vrunk11/DomesdayDuplicator/hardware/pcb/ADC.kicad_sch

## KiCad design hardware/pcb/ADC.kicad_sch (2026-08-29)

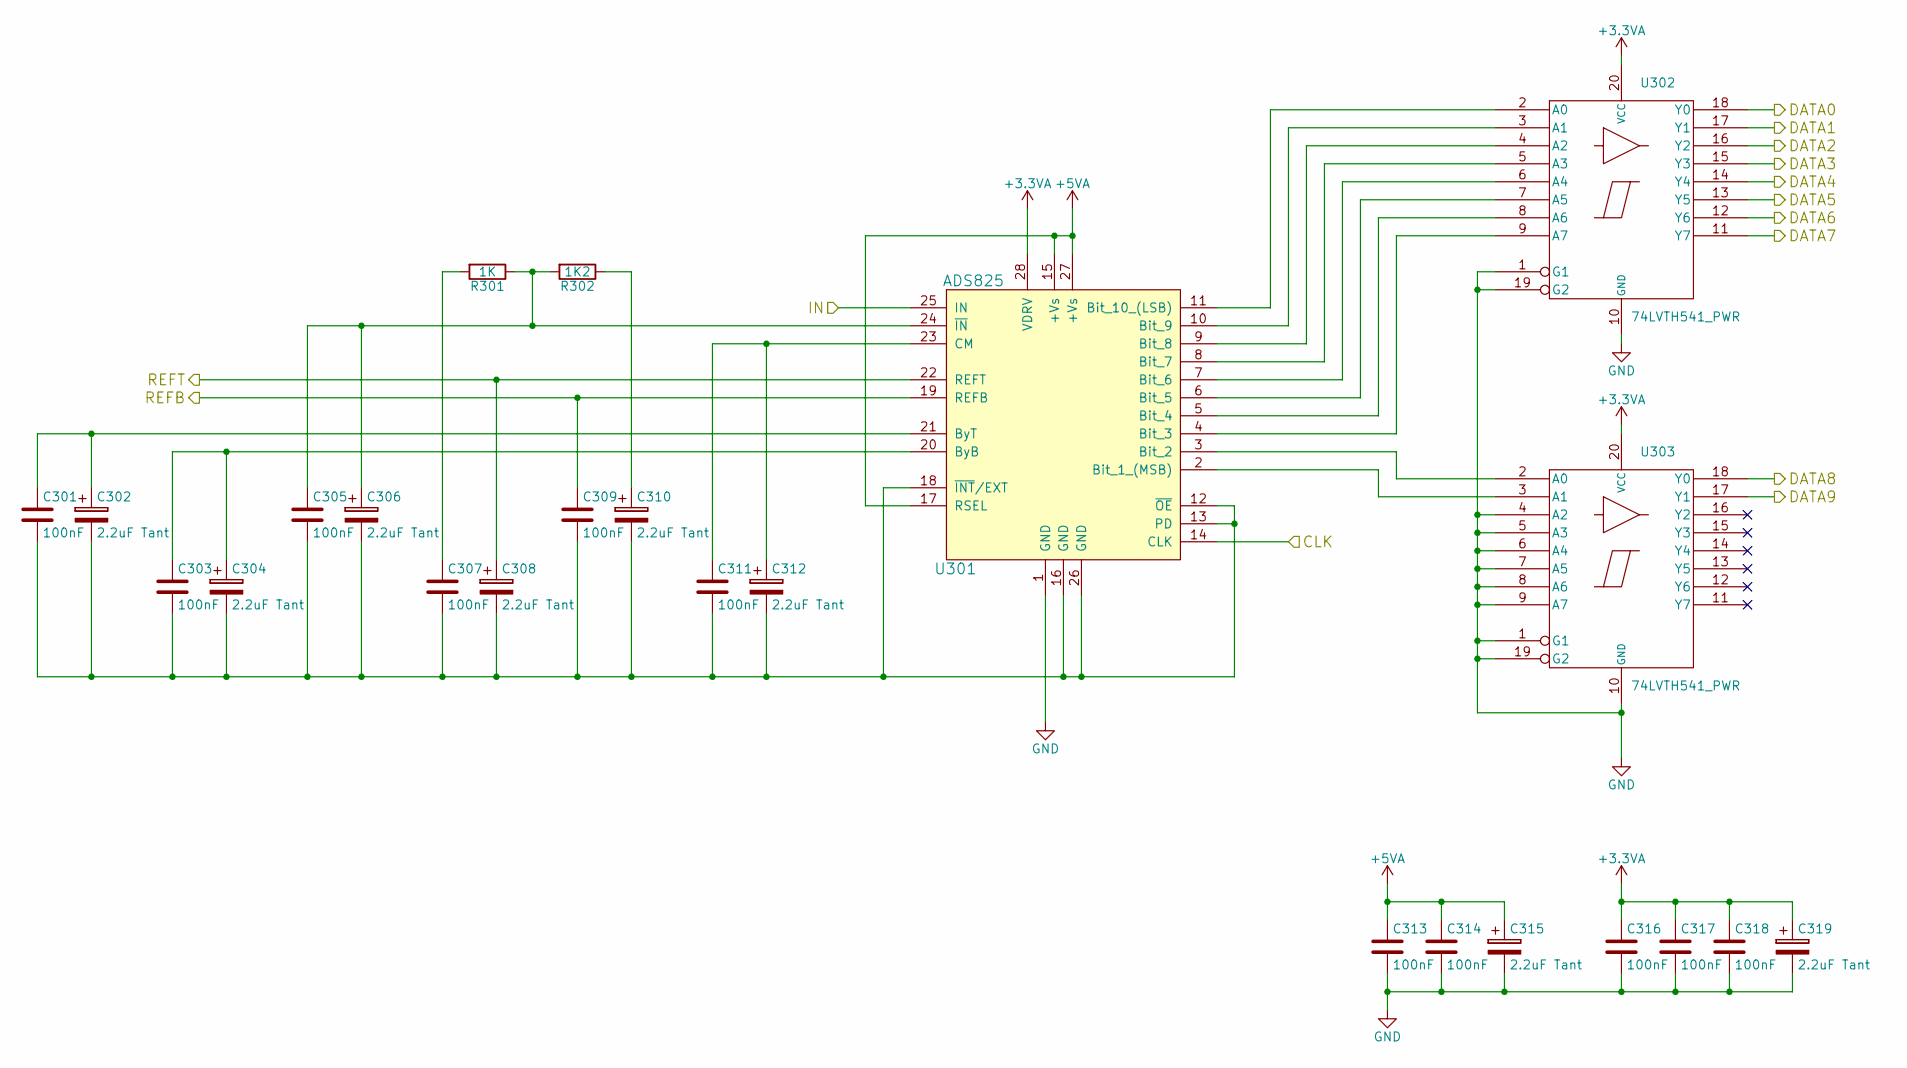
[picture p8: schematic ADC.kicad_sch]

Parts:
C301, C303, C305, C307, C309, C311, C313, C314, C316, C317, C318: 100nF; C_0805
C302, C304, C306, C308, C310, C312, C315, C319: 2.2uF Tant; CP_Tantalum_Case-A_EIA-3216-18_Reflow
R301: 1K; R_0805
R302: 1K2; R_0805
U301: ADS825; SSOP-28_5.3x10.2mm_Pitch0.65mm
U302, U303: 74LVTH541_PWR; TSSOP-20_4.4x6.5mm_Pitch0.65mm

Connections:
+3.3VA: C316.1, C317.1, C318.1, C319.1, U301.28 (VDRV), U302.20 (VCC), U303.20 (VCC)
+5VA: C313.1, C314.1, C315.1, U301.15 (+Vs), U301.17 (RSEL), U301.27 (+Vs)
CLK: U301.14 (CLK)
DATA0: U302.18 (Y0)
DATA1: U302.17 (Y1)
DATA2: U302.16 (Y2)
DATA3: U302.15 (Y3)
DATA4: U302.14 (Y4)
DATA5: U302.13 (Y5)
DATA6: U302.12 (Y6)
DATA7: U302.11 (Y7)
DATA8: U303.18 (Y0)
DATA9: U303.17 (Y1)
GND: C313.2, C314.2, C315.2, C316.2, C317.2, C318.2, C319.2, U301.1 (GND), U302.1 (G1), U302.10 (GND), U302.19 (G2), U303.1 (G1), U303.4 (A2), U303.5 (A3), U303.6 (A4), U303.7 (A5), U303.8 (A6), U303.9 (A7), U303.10 (GND), U303.19 (G2)
IN: U301.25 (IN)
unnamed: C301.1, C302.1, U301.21 (ByT)
unnamed: C301.2, C302.2, C303.2, C304.2, C305.2, C306.2, C307.2, C308.2, C309.2, C310.2, C311.2, C312.2, U301.12 (~OE), U301.13 (PD), U301.16 (GND), U301.18 (~INT/EXT), U301.26 (GND)
unnamed: C303.1, C304.1, U301.20 (ByB)
unnamed: C305.1, C306.1, R301.1, R302.2, U301.24 (~IN)
unnamed: C307.1, R301.2
unnamed: C310.1, R302.1
unnamed: C311.1, C312.1, U301.23 (CM)
unnamed: U301.2 (Bit_1_(MSB)), U303.3 (A1)
unnamed: U301.3 (Bit_2), U303.2 (A0)
unnamed: U301.4 (Bit_3), U302.9 (A7)
unnamed: U301.5 (Bit_4), U302.8 (A6)
unnamed: U301.6 (Bit_5), U302.7 (A5)
unnamed: U301.7 (Bit_6), U302.6 (A4)
unnamed: U301.8 (Bit_7), U302.5 (A3)
unnamed: U301.9 (Bit_8), U302.4 (A2)
unnamed: U301.10 (Bit_9), U302.3 (A1)
unnamed: U301.11 (Bit_10_(LSB)), U302.2 (A0)
REFB: C309.1, U301.19 (REFB)
REFT: C308.1, U301.22 (REFT)
