vrunk11/DomesdayDuplicator/hardware/pcb/Domesday Duplicator.kicad_sch

## KiCad design hardware/pcb/Domesday Duplicator.kicad_sch (2026-08-29)

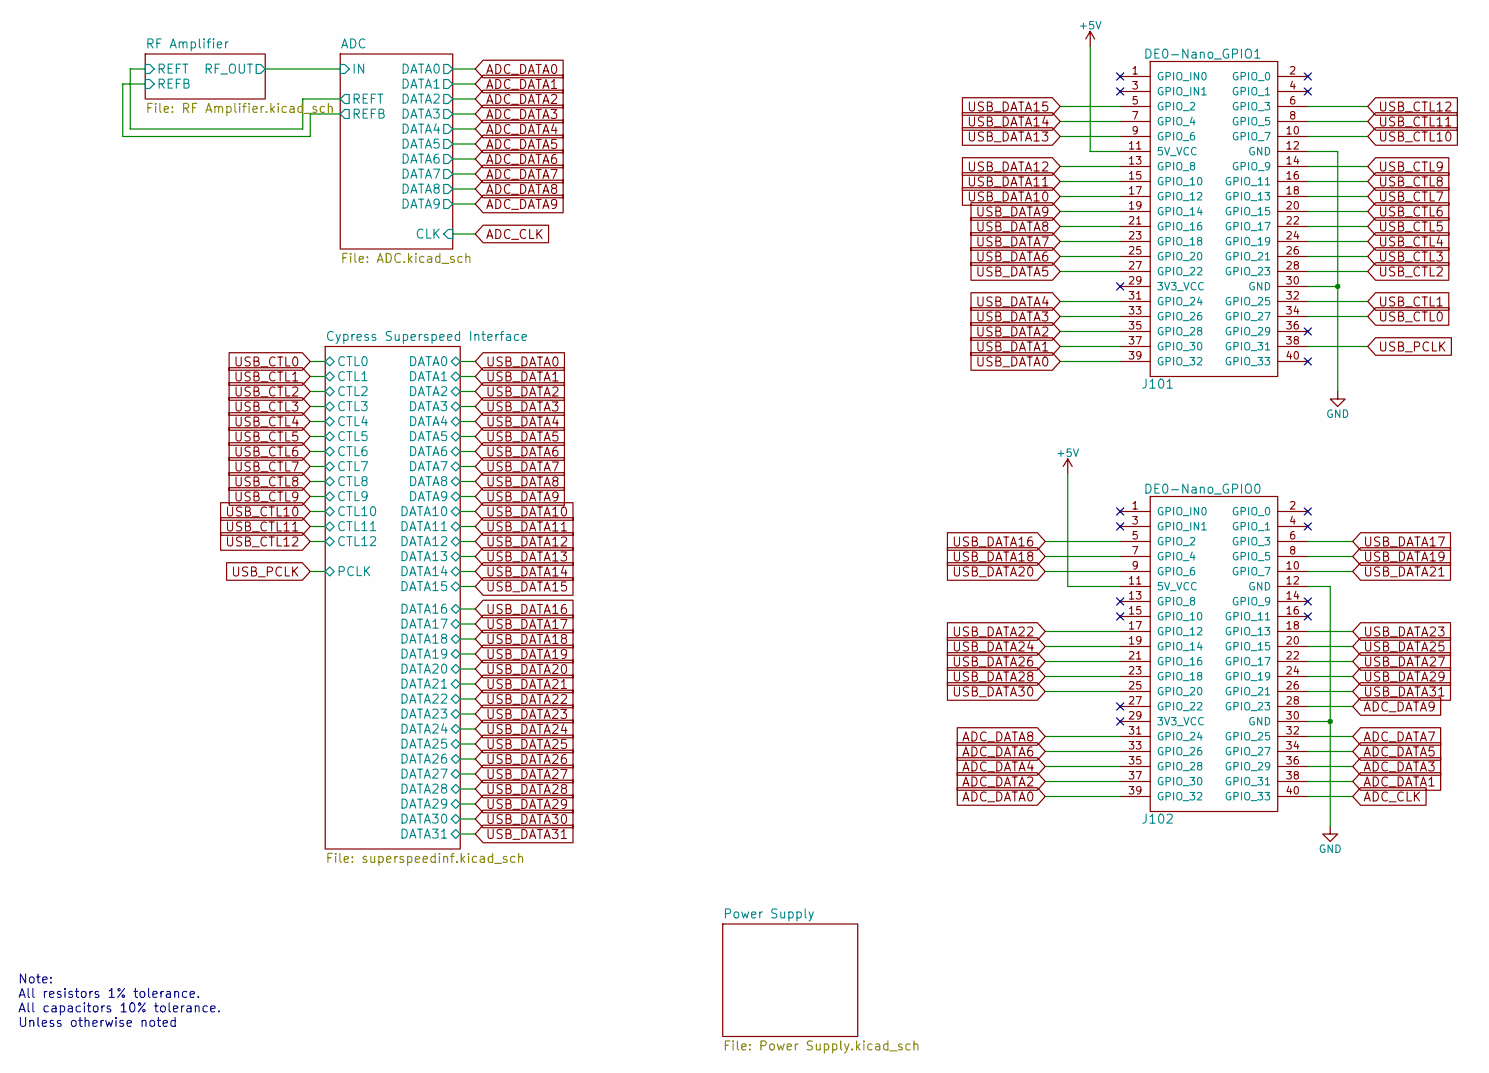
[picture p9: schematic Domesday Duplicator.kicad_sch]

Parts:
J101: DE0-Nano_GPIO1; Socket_Strip_Straight_2x20_Pitch2.54mm
J102: DE0-Nano_GPIO0; Socket_Strip_Straight_2x20_Pitch2.54mm

Connections:
+5V: J101.11 (5V_VCC), J102.11 (5V_VCC)
ADC_CLK: J102.40 (GPIO_33)
ADC_DATA0: J102.39 (GPIO_32)
ADC_DATA1: J102.38 (GPIO_31)
ADC_DATA2: J102.37 (GPIO_30)
ADC_DATA3: J102.36 (GPIO_29)
ADC_DATA4: J102.35 (GPIO_28)
ADC_DATA5: J102.34 (GPIO_27)
ADC_DATA6: J102.33 (GPIO_26)
ADC_DATA7: J102.32 (GPIO_25)
ADC_DATA8: J102.31 (GPIO_24)
ADC_DATA9: J102.28 (GPIO_23)
GND: J101.12 (GND), J101.30 (GND), J102.12 (GND), J102.30 (GND)
USB_CTL0: J101.34 (GPIO_27)
USB_CTL1: J101.32 (GPIO_25)
USB_CTL2: J101.28 (GPIO_23)
USB_CTL3: J101.26 (GPIO_21)
USB_CTL4: J101.24 (GPIO_19)
USB_CTL5: J101.22 (GPIO_17)
USB_CTL6: J101.20 (GPIO_15)
USB_CTL7: J101.18 (GPIO_13)
USB_CTL8: J101.16 (GPIO_11)
USB_CTL9: J101.14 (GPIO_9)
USB_CTL10: J101.10 (GPIO_7)
USB_CTL11: J101.8 (GPIO_5)
USB_CTL12: J101.6 (GPIO_3)
USB_DATA0: J101.39 (GPIO_32)
USB_DATA1: J101.37 (GPIO_30)
USB_DATA2: J101.35 (GPIO_28)
USB_DATA3: J101.33 (GPIO_26)
USB_DATA4: J101.31 (GPIO_24)
USB_DATA5: J101.27 (GPIO_22)
USB_DATA6: J101.25 (GPIO_20)
USB_DATA7: J101.23 (GPIO_18)
USB_DATA8: J101.21 (GPIO_16)
USB_DATA9: J101.19 (GPIO_14)
USB_DATA10: J101.17 (GPIO_12)
USB_DATA11: J101.15 (GPIO_10)
USB_DATA12: J101.13 (GPIO_8)
USB_DATA13: J101.9 (GPIO_6)
USB_DATA14: J101.7 (GPIO_4)
USB_DATA15: J101.5 (GPIO_2)
USB_DATA16: J102.5 (GPIO_2)
USB_DATA17: J102.6 (GPIO_3)
USB_DATA18: J102.7 (GPIO_4)
USB_DATA19: J102.8 (GPIO_5)
USB_DATA20: J102.9 (GPIO_6)
USB_DATA21: J102.10 (GPIO_7)
USB_DATA22: J102.17 (GPIO_12)
USB_DATA23: J102.18 (GPIO_13)
USB_DATA24: J102.19 (GPIO_14)
USB_DATA25: J102.20 (GPIO_15)
USB_DATA26: J102.21 (GPIO_16)
USB_DATA27: J102.22 (GPIO_17)
USB_DATA28: J102.23 (GPIO_18)
USB_DATA29: J102.24 (GPIO_19)
USB_DATA30: J102.25 (GPIO_20)
USB_DATA31: J102.26 (GPIO_21)
USB_PCLK: J101.38 (GPIO_31)

Notes on the sheet:
Note: All resistors 1% tolerance. All capacitors 10% tolerance. Unless otherwise noted
