vrunk11/DomesdayDuplicator/hardware/pcb/Power Supply.kicad_sch

## KiCad design hardware/pcb/Power Supply.kicad_sch (2026-08-29)

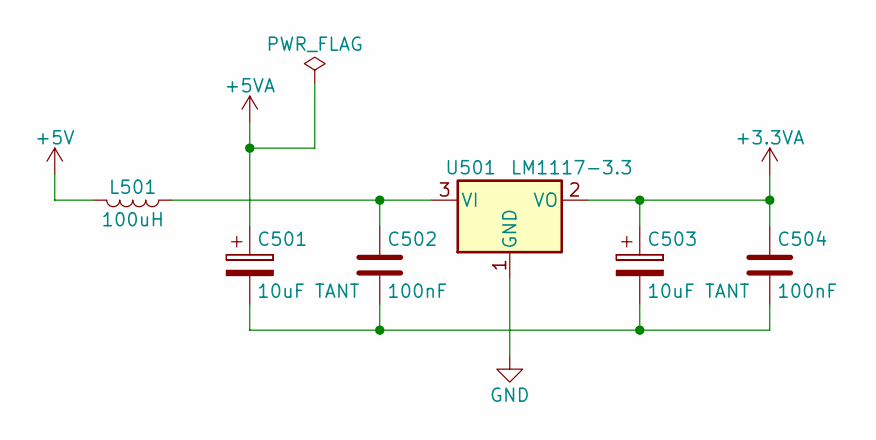
[picture p10: schematic Power Supply.kicad_sch]

Parts:
C501, C503: 10uF TANT; CP_Tantalum_Case-B_EIA-3528-21_Reflow
C502, C504: 100nF; C_0805
L501: 100uH; Inductor_Bourns-SRU8043
U501: LM1117-3.3; SOT-223-3_TabPin2

Connections:
+3.3VA: C503.1, C504.1, U501.2 (VO)
+5V: L501.2
+5VA: C501.1
GND: U501.1 (GND)
unnamed: C501.2, C502.2, C503.2, C504.2
unnamed: C502.1, L501.1, U501.3 (VI)
