vrunk11/DomesdayDuplicator/hardware/pcb/RF Amplifier.kicad_sch

## KiCad design hardware/pcb/RF Amplifier.kicad_sch (2026-08-29)

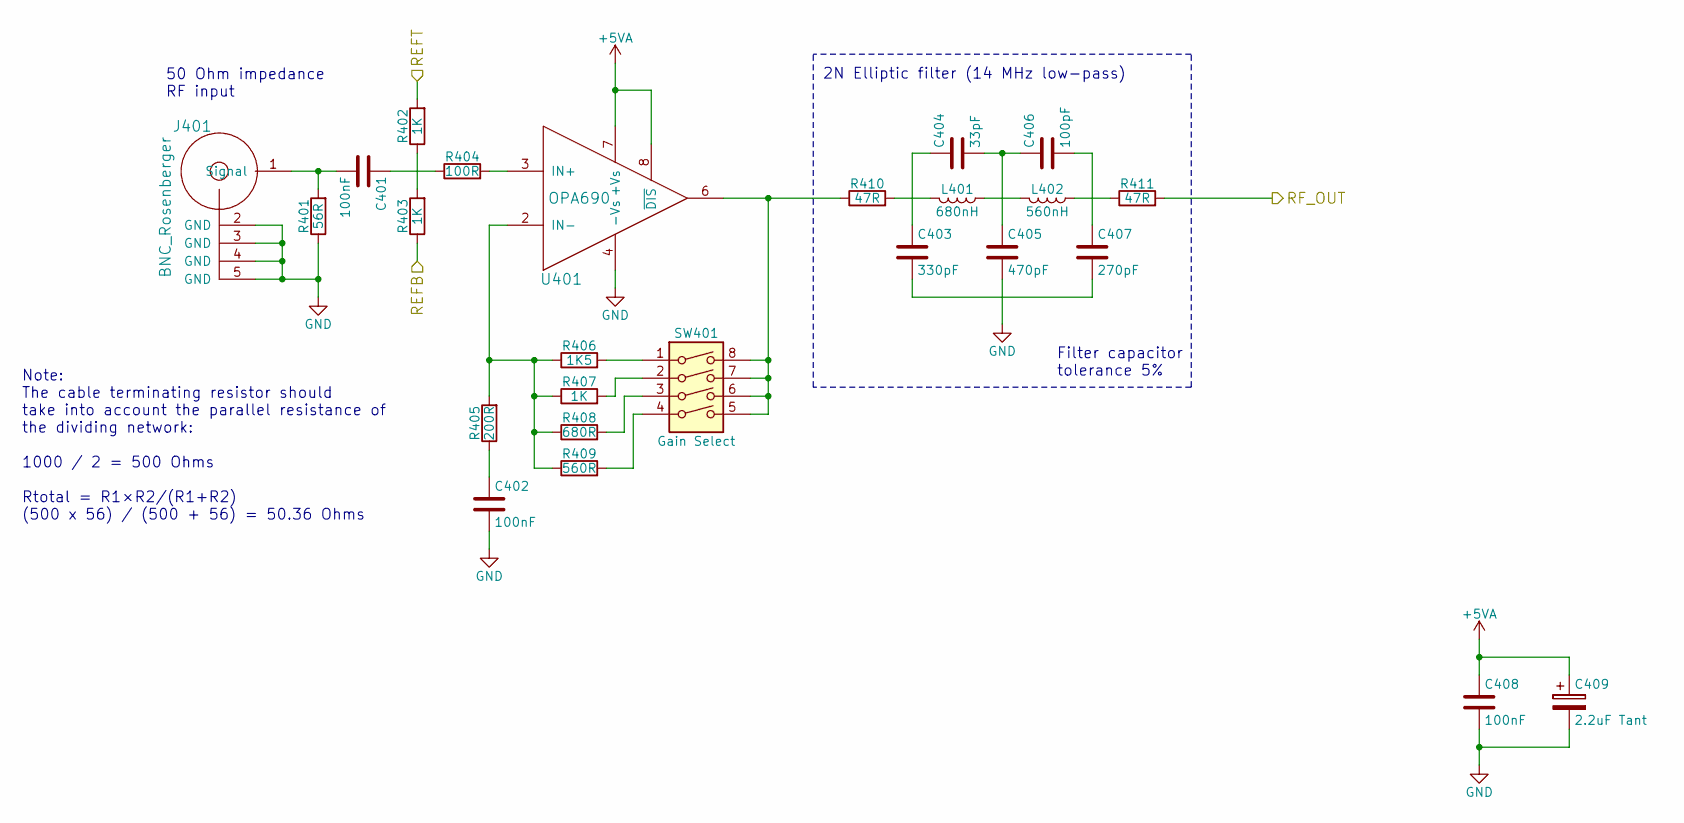
[picture p11: schematic RF Amplifier.kicad_sch]

Parts:
C401, C402, C408: 100nF; C_0805
C403: 330pF; C_0805
C404: 33pF; C_0805
C405: 470pF; C_0805
C406: 100pF; C_0805
C407: 270pF; C_0805
C409: 2.2uF Tant; CP_Tantalum_Case-A_EIA-3216-18_Reflow
J401: BNC_Rosenberger; BNC Socket
L401: 680nH; L_0805
L402: 560nH; L_0805
R401: 56R; R_0805
R402, R403, R407: 1K; R_0805
R404: 100R; R_0805
R405: 200R; R_0805
R406: 1K5; R_0805
R408: 680R; R_0805
R409: 560R; R_0805
R410, R411: 47R; R_0805
SW401: Gain Select; SW_DIP_x4_W7.62mm_Slide_Copal_CHS-B
U401: OPA690; SOIC-8_3.9x4.9mm_Pitch1.27mm

Connections:
+5VA: C408.1, C409.1, U401.7 (+Vs), U401.8 (~DIS)
GND: C402.2, C405.2, C408.2, C409.2, J401.2 (GND), J401.3 (GND), J401.4 (GND), J401.5 (GND), R401.1, U401.4 (-Vs)
unnamed: C401.1, R404.1
unnamed: C401.2, J401.1 (Signal), R401.2
unnamed: C402.1, R405.1
unnamed: C403.1, C404.1
unnamed: C403.2, C407.2
unnamed: C404.2, C405.1, C406.1
unnamed: C406.2, C407.1
unnamed: L401.1, L402.2
unnamed: L401.2, R410.2
unnamed: L402.1, R411.1
unnamed: R402.1, R403.2
unnamed: R404.2, U401.3 (IN+)
unnamed: R405.2, R406.1, R407.1, R408.1, R409.1, U401.2 (IN-)
unnamed: R406.2, SW401.1
unnamed: R407.2, SW401.2
unnamed: R408.2, SW401.3
unnamed: R409.2, SW401.4
unnamed: R410.1, SW401.5, SW401.6, SW401.7, SW401.8, U401.6 (Output)
REFB: R403.1
REFT: R402.2
RF_OUT: R411.2

Notes on the sheet:
Note: The cable terminating resistor should take into account the parallel resistance of the dividing network: 1000 / 2 = 500 Ohms Rtotal = R1×R2/(R1+R2) (500 x 56) / (500 + 56) = 50.36 Ohms
Filter capacitor tolerance 5%
2N Elliptic filter (14 MHz low-pass)
50 Ohm impedance RF input
