vrunk11/DomesdayDuplicator/hardware/pcb/superspeedinf.kicad_sch

## KiCad design hardware/pcb/superspeedinf.kicad_sch (2026-08-29)

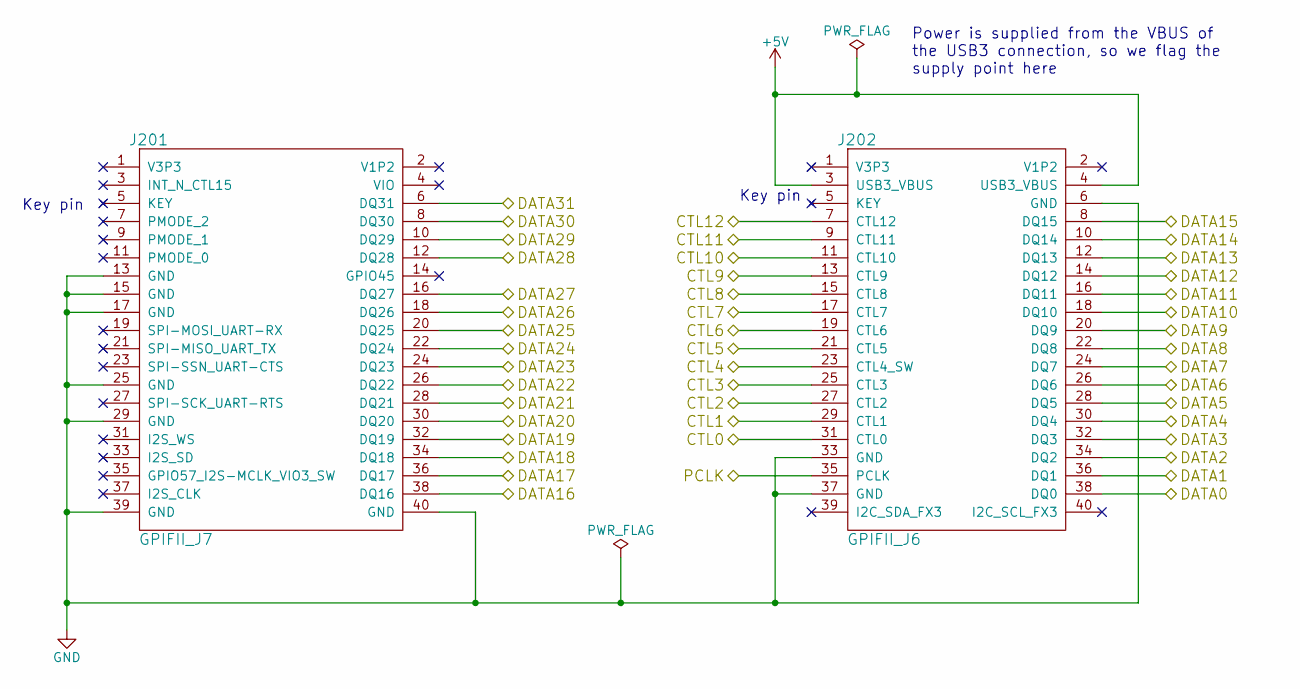
[picture p12: schematic superspeedinf.kicad_sch]

Parts:
J201: GPIFII_J7; Pin_Header_Straight_2x20_Pitch2.54mm
J202: GPIFII_J6; Pin_Header_Straight_2x20_Pitch2.54mm

Connections:
+5V: J202.3 (USB3_VBUS), J202.4 (USB3_VBUS)
CTL0: J202.31 (CTL0)
CTL1: J202.29 (CTL1)
CTL2: J202.27 (CTL2)
CTL3: J202.25 (CTL3)
CTL4: J202.23 (CTL4_SW)
CTL5: J202.21 (CTL5)
CTL6: J202.19 (CTL6)
CTL7: J202.17 (CTL7)
CTL8: J202.15 (CTL8)
CTL9: J202.13 (CTL9)
CTL10: J202.11 (CTL10)
CTL11: J202.9 (CTL11)
CTL12: J202.7 (CTL12)
DATA0: J202.38 (DQ0)
DATA1: J202.36 (DQ1)
DATA2: J202.34 (DQ2)
DATA3: J202.32 (DQ3)
DATA4: J202.30 (DQ4)
DATA5: J202.28 (DQ5)
DATA6: J202.26 (DQ6)
DATA7: J202.24 (DQ7)
DATA8: J202.22 (DQ8)
DATA9: J202.20 (DQ9)
DATA10: J202.18 (DQ10)
DATA11: J202.16 (DQ11)
DATA12: J202.14 (DQ12)
DATA13: J202.12 (DQ13)
DATA14: J202.10 (DQ14)
DATA15: J202.8 (DQ15)
DATA16: J201.38 (DQ16)
DATA17: J201.36 (DQ17)
DATA18: J201.34 (DQ18)
DATA19: J201.32 (DQ19)
DATA20: J201.30 (DQ20)
DATA21: J201.28 (DQ21)
DATA22: J201.26 (DQ22)
DATA23: J201.24 (DQ23)
DATA24: J201.22 (DQ24)
DATA25: J201.20 (DQ25)
DATA26: J201.18 (DQ26)
DATA27: J201.16 (DQ27)
DATA28: J201.12 (DQ28)
DATA29: J201.10 (DQ29)
DATA30: J201.8 (DQ30)
DATA31: J201.6 (DQ31)
GND: J201.13 (GND), J201.15 (GND), J201.17 (GND), J201.25 (GND), J201.29 (GND), J201.39 (GND), J201.40 (GND), J202.6 (GND), J202.33 (GND), J202.37 (GND)
PCLK: J202.35 (PCLK)

Notes on the sheet:
Key pin
Power is supplied from the VBUS of the USB3 connection, so we flag the supply point here
