vrunk11/DomesdayDuplicator/ddd-gui/src/gui/bringup_text.cpp

/************************************************************************

    bringup_text.cpp

    What the bring-up wizard says, in one place
    Domesday Duplicator - LaserDisc RF sampler
    SPDX-FileCopyrightText: 2026 Simon Inns
    SPDX-License-Identifier: GPL-3.0-or-later

************************************************************************/

#include "bringup_text.h"

#include <QCoreApplication>
#include <QStringList>
#include <string>

#include "firmware_version.h"
#include "update_gate.h"
#include "wire_protocol.h"

namespace ddd::gui {
namespace {

QString Translate(const char* text) {
  return QCoreApplication::translate("BringUpText", text);
}

// The one sentence that appears on every page asking for a power cycle, and
// the reason it is a function rather than three copies of a string: if it is
// ever reworded it has to be reworded everywhere, because a user who reads
// "unplug both cables" once and "unplug the cable" the next time has been
// given permission to do the thing that silently does nothing.
QString BothCables() {
  return Translate(
      "Unplug <b>both</b> USB cables — the kit's USB 3.0 cable and the "
      "DE0-Nano's mini-USB. Either one on its own keeps the unit powered, so "
      "pulling only one changes nothing while the board stays lit and looks "
      "perfectly normal.");
}

// One mark, in its colour. The rows, the legend, the verification list and
// both status lines all draw their marks through here, so a tick can never
// mean one thing in one place and another somewhere else.
QString Marked(BringUpRowState state) {
  return QStringLiteral("<span style=\"color:%1\"><b>%2</b></span>")
      .arg(BringUpMarkColour(state), BringUpMark(state));
}

// How long a step takes, said the way somebody deciding whether to wait would
// say it. The estimates arrive as a number of seconds, and under a couple of
// minutes that is exactly what a user wants — "about 40 seconds" is a wait to
// sit through. Past that it stops being readable: "about 236 seconds" asks
// the reader to do the division themselves before they know whether they have
// time to make a cup of tea, so anything longer is rounded to the nearest
// minute and said in minutes.
//
// The rounding is deliberately coarse. These are estimates from a bytes-per-
// second rate, not measurements, and a figure quoted to the second invites a
// user to treat a bar that runs ten seconds over as something having gone
// wrong.
QString DurationPhrase(int seconds) {
  if (seconds < 120) {
    return Translate("%1 seconds").arg(seconds);
  }
  return Translate("%1 minutes").arg((seconds + 30) / 60);
}

}  // namespace

QString BringUpPageTitle(BringUpPage page) {
  switch (page) {
    case BringUpPage::kOverview:
      return Translate("1 of 8");
    case BringUpPage::kConnect:
      return Translate("2 of 8");
    case BringUpPage::kImage:
      return Translate("3 of 8");
    case BringUpPage::kConfigure:
      return Translate("4 of 8");
    case BringUpPage::kProgram:
      return Translate("5 of 8");
    case BringUpPage::kRemoveJumper:
      return Translate("6 of 8");
    case BringUpPage::kPowerCycle:
      return Translate("7 of 8");
    case BringUpPage::kVerify:
      return Translate("8 of 8");
  }
  return QString();
}

QString BringUpPageHeading(BringUpPage page) {
  switch (page) {
    case BringUpPage::kOverview:
      return Translate("What this does, and what it will ask of you");
    case BringUpPage::kConnect:
      return Translate("Both boards, and jumper J4");
    case BringUpPage::kImage:
      return Translate("The update file");
    case BringUpPage::kConfigure:
      return Translate("Load the gateware into the FPGA");
    case BringUpPage::kProgram:
      return Translate("Program the board");
    case BringUpPage::kRemoveJumper:
      return Translate("Remove jumper J4");
    case BringUpPage::kPowerCycle:
      return Translate("Power cycle");
    case BringUpPage::kVerify:
      return Translate("What the device is running now");
  }
  return QString();
}

QString BringUpOverviewText() {
  return Translate(
      "<p>This programs a Domesday Duplicator completely — the FX3's firmware, "
      "and both images in the FPGA's configuration flash. At the end the board "
      "is ready to capture, and there is nothing to do afterwards.</p>"

      "<p><b>Have these ready before you start:</b></p>"

      "<ul>"
      "<li>the unit <b>out of its enclosure</b> — the DE0-Nano's mini-USB "
      "connector cannot be reached with the case on;</li>"
      "<li><b>both cables connected</b>, the kit's USB 3.0 cable and the "
      "DE0-Nano's mini-USB, and left connected throughout;</li>"
      "<li>a <b>jumper</b> for the FX3's two-pin PMODE header — needed "
      "whatever the board is running, including one that has never been "
      "programmed;</li>"
      "<li>an <b>update file</b> — this application normally carries one, and "
      "step 3 says so if it does not.</li>"
      "</ul>"

      "<p><b>You will be asked to:</b> fit a jumper, unplug both cables and "
      "reconnect them, press two buttons, remove the jumper, unplug both "
      "cables and reconnect them once more, and take the mini-USB off at the "
      "end. Nothing physical is asked for twice.</p>"

      "<p><b>It does not matter what the board is running now</b>, and running "
      "this twice is harmless.</p>");
}

QString BringUpDurationText() {
  return Translate(
      "About five minutes, most of it spent writing and checking the three "
      "images.");
}

QString BringUpWaitingText(const QString& what) {
  return QStringLiteral("<p>%1 <b>%2</b> %3</p>")
      .arg(Marked(BringUpRowState::kWaiting), Translate("Waiting for"), what);
}

QString BringUpStepDoneText(const QString& what) {
  // **All done** first, and the button to press last. Everything a user
  // wants off a finished step is at the two ends of one short line: whether it
  // worked, and what to do about it. What actually happened goes in the
  // middle, where it can be read by somebody who wants it and skipped by
  // somebody who does not.
  QString text =
      QStringLiteral("<p>%1 <b>%2</b>")
          .arg(Marked(BringUpRowState::kReady), Translate("All done."));
  if (!what.isEmpty()) {
    text += QStringLiteral(" ") + what;
  }
  return text + QStringLiteral(" <b>") +
         Translate("Click “Next ›” to continue.") + QStringLiteral("</b></p>");
}

// --- the connectivity page ------------------------------------------------

QString BringUpMark(BringUpRowState state) {
  switch (state) {
    case BringUpRowState::kReady:
      return QStringLiteral("✓");
    case BringUpRowState::kWaiting:
      return QStringLiteral("•");
    case BringUpRowState::kProblem:
      return QStringLiteral("✕");
  }
  return QStringLiteral("✕");
}

QString BringUpMarkColour(BringUpRowState state) {
  switch (state) {
    case BringUpRowState::kReady:
      return QStringLiteral("#27ae60");
    case BringUpRowState::kWaiting:
      return QStringLiteral("#d68910");
    case BringUpRowState::kProblem:
      return QStringLiteral("#c0392b");
  }
  return QStringLiteral("#c0392b");
}

QString BringUpConnectLegend() {
  // The amber case is the one worth the words. A coloured mark that is not
  // green reads as a fault, and here it usually is not: it means the board is
  // in a state the wizard already expects, and that the three steps above are
  // what take it out of that state.
  return Translate(
             "<p>%1 means that board is ready. %2 means it is there and the "
             "steps above have still to be done to it — and <b>not</b> that "
             "anything is wrong with it. "
             "%3 is something to put right before going on.</p>")
      .arg(Marked(BringUpRowState::kReady), Marked(BringUpRowState::kWaiting),
           Marked(BringUpRowState::kProblem));
}

BringUpStatusRow BringUpFx3Row(const std::optional<capture::DeviceInfo>& fx3,
                               capture::UsbPresence debug_bridge,
                               bool restarted) {
  BringUpStatusRow row;
  row.title = Translate("FX3 board (SuperSpeed Explorer Kit)");

  if (fx3.has_value()) {
    // The commit the running firmware reports, when it reports one. Naming it
    // is what separates "this is the build you just installed" from "this is
    // some firmware or other", which is the whole of what somebody looking at
    // this row wants to know.
    const std::optional<std::string> commit =
        capture::ParseFirmwareCommit(fx3->product_string);
    const QString named =
        commit.has_value()
            ? Translate(" (%1)").arg(QString::fromStdString(*commit))
            : QString();

    switch (fx3->personality) {
      case capture::DevicePersonality::kRecovery:
        // The one state this page is waiting for — but only once the board has
        // been seen to restart, and the sentence says why. An FX3 whose EEPROM
        // has never been written sits here jumper or no jumper, so "already in
        // the boot ROM" is not "already arranged": without a jumper holding it
        // there, such a board leaves again at the first restart.
        if (restarted) {
          row.state = BringUpRowState::kReady;
          row.detail = Translate(
              "In its boot ROM after restarting, which is where the rest of "
              "this needs it and what says jumper J4 is fitted.");
          return row;
        }

        row.state = BringUpRowState::kWaiting;
        row.detail = Translate(
            "Waiting in its boot ROM, which is where this needs it — most "
            "likely a newly built kit, whose EEPROM is empty. <b>Fit the "
            "jumper and pull both cables anyway:</b> an empty board comes up "
            "here whether or not one is fitted, and without it the board "
            "would leave the boot ROM part way through the programming. This "
            "row ticks when the board has been seen to go away and come "
            "back.");
        return row;

      case capture::DevicePersonality::kApplication:
        row.state = BringUpRowState::kWaiting;
        if (capture::ProtocolVersionIsSupported(fx3->protocol_version)) {
          // A board that already works. Somebody who only wants to update it
          // is in the wrong window, and the row says so rather than leading
          // them through the whole procedure to find out.
          row.detail =
              Translate(
                  "Running this application's own firmware%1, so this board "
                  "does not need bringing up. If you only want to update it, "
                  "close this and use <b>Tools ▸ Firmware ▸ Update "
                  "firmware…</b> instead, which needs no cables moved and no "
                  "case opened. Carrying on here is safe and reprograms "
                  "everything — fit jumper J4 and pull both cables, as above, "
                  "and it will come back in its boot ROM.")
                  .arg(named);
        } else {
          // Out of range in *either* direction, and the reachable direction is
          // newer rather than older: an application can easily be older than
          // the firmware in front of it. Firmware older than the update agent
          // but under these identifiers was never released — it exists only as
          // an intermediate build inside the repository — so this says what is
          // actually known rather than naming a generation of firmware nobody
          // has.
          row.detail =
              Translate(
                  "Running Duplicator firmware%1 whose protocol this build of "
                  "the application does not know, most likely newer than it. "
                  "Bring-up replaces it with the firmware from the file you "
                  "choose, so this is safe to carry on with — fit jumper J4 "
                  "and pull both cables, as above.")
                  .arg(named);
        }
        return row;

      case capture::DevicePersonality::kLegacy:
        row.state = BringUpRowState::kWaiting;
        row.detail = Translate(
            "Running the <b>original</b> Duplicator firmware — the one from "
            "before this application existed, enumerating as 1d50:603b. This "
            "is exactly what this wizard is for. Fit jumper J4 and pull both "
            "cables, as above, and it will come back in its boot ROM as "
            "04b4:00f3.");
        return row;

      case capture::DevicePersonality::kFlashProgrammer:
        row.state = BringUpRowState::kProblem;
        row.detail = Translate(
            "Running the Cypress secondary loader, left in memory by a "
            "programming session that did not finish. Unplug both USB cables, "
            "wait a moment and reconnect them.");
        return row;
    }
  }

  if (debug_bridge == capture::UsbPresence::kPresent) {
    row.state = BringUpRowState::kProblem;
    row.detail = Translate(
        "The kit's debug serial port is answering, so the board has power — "
        "but nothing is answering on the USB 3.0 link. Check that cable, and "
        "that it is in a USB 3.0 socket.");
    return row;
  }

  // Nothing on the bus — and on Windows that includes a board which is
  // plainly there. This application sees a device there only when its USB
  // identifier is bound to WinUSB, and a board running firmware presents an
  // identifier nobody has any reason to bind: the original 1d50:603b above
  // all. So an empty row is not evidence that nothing is attached, and the
  // remedy is the one the page has already asked for — the jumper, whose
  // 04b4:00f3 is an identifier this flow needs bound in any case.
  row.state = BringUpRowState::kProblem;
  row.detail = Translate(
      "Nothing found. Connect the kit's USB 3.0 cable, fit jumper J4 and pull "
      "both cables, as above. <b>On Windows a board running firmware is "
      "invisible here until the jumper is fitted</b>: the application sees "
      "only devices whose USB identifier is bound to WinUSB, and a board "
      "running the original firmware presents 1d50:603b, which nothing binds "
      "— the boot ROM's 04b4:00f3 is the identifier to bind, and the jumper "
      "is what produces it. On Linux, check that the device rules are "
      "installed (fx3/programmer/configs/70-domesday-duplicator.rules).");
  return row;
}

BringUpStatusRow BringUpFpgaRow(bool opened, capture::UsbPresence presence,
                                const QString& problem) {
  BringUpStatusRow row;
  row.title = Translate("FPGA board (DE0-Nano, on-board USB-Blaster)");

  if (opened) {
    row.state = BringUpRowState::kReady;
    row.detail = Translate("Found and opened.");
    return row;
  }

  row.state = BringUpRowState::kProblem;

  // Attached and unopenable is a different problem from absent, and it is the
  // one with a remedy the user can act on. The cable driver's own sentence
  // says which — Quartus's jtagd holding it, the udev rules on Linux, the
  // driver binding on Windows.
  if (presence == capture::UsbPresence::kPresent) {
    row.detail =
        problem.isEmpty()
            ? Translate(
                  "A USB-Blaster is attached but could not be opened. On Linux "
                  "this is the udev rules "
                  "(fx3/programmer/configs/70-domesday-duplicator.rules); on "
                  "Windows it is the driver binding. Quartus's own jtagd holds "
                  "the cable open whenever it is running.")
            : problem;
    return row;
  }

  // The charge-only cable first, and deliberately: it is the documented
  // failure of this exact step, and in an assembled unit it is especially
  // misleading, because the board is lit from the USB 3.0 side no matter what
  // the mini-USB is doing.
  row.detail = Translate(
      "Nothing found on the DE0-Nano's mini-USB connector. The commonest cause "
      "is a charge-only cable, which carries power and no data — and the board "
      "will be lit either way, because the USB 3.0 cable is powering it. Try a "
      "cable you know carries data, then check the connector itself.");
  if (!problem.isEmpty()) {
    row.detail += QStringLiteral("<br><br>") + problem;
  }
  return row;
}

QString BringUpConnectText() {
  return Translate(
             "<p><b>1. Fit jumper J4</b> on the FX3 board — the two-pin "
             "<tt>PMODE</tt> header, photographed at the foot of this page. "
             "<b>Fit it whatever the board is running</b>, including one "
             "already reported below as waiting in its boot ROM. A board "
             "whose EEPROM has never been written comes up there with or "
             "without the jumper — and one that got there without it leaves "
             "again at the first restart, part way through the writing, which "
             "is where the bring-up fails. The jumper is what makes the boot "
             "ROM the place the board comes back to every time.</p>"

             "<p><b>2. </b>") +
         BothCables() + QStringLiteral("</p>") +
         Translate(
             "<p><b>3. Plug both back in</b> — the kit's USB 3.0 cable and "
             "the DE0-Nano's mini-USB — and leave both connected until the "
             "end.</p>"

             "<p>The jumper only takes effect when the board boots, and the "
             "unit does not boot while either cable is still feeding it — "
             "which is why both have to come out. What this page then waits "
             "for is the FX3 back in its <b>boot ROM</b>, which is the one "
             "state the rest of this can work from, and reached the same way "
             "from a bare kit, a legacy unit and a board that already "
             "works.</p>"

             "<p>Each board is <b>opened</b> here rather than merely noticed, "
             "so that a permissions problem turns up now rather than in the "
             "middle of writing a flash.</p>");
}

// --- the physical pages ---------------------------------------------------

QString BringUpRemoveJumperText() {
  return Translate(
      "<p><b>Remove jumper J4</b> from the FX3 board — the same header as "
      "before, bare this time, as shown below.</p>"

      "<p><b>Do not unplug anything yet.</b> There is one power cycle on the "
      "next page and it does everything.</p>");
}

QString BringUpPowerCycleText() {
  return Translate("<p><b>1. </b>") + BothCables() + QStringLiteral("</p>") +
         Translate(
             "<p><b>2. Wait a couple of seconds.</b></p>"

             "<p><b>3. Plug both back in.</b></p>"

             "<p>This is what makes the three images you have just written the "
             "running ones: the FX3 re-reads where it boots from, and the FPGA "
             "loads the factory image, which hands over to the application "
             "image beside it.</p>");
}

QString BringUpPowerCycleTimeoutText() {
  return Translate(
      "<p><b>Did both cables come out?</b> That is nearly always what this "
      "is. Either cable on its own keeps the unit powered, so if one stayed "
      "in, nothing rebooted — and the board will have looked exactly as it "
      "should throughout.</p>"

      "<p>Unplug both, count to three, and reconnect them.</p>"

      "<p>If it still does not come back: the jumper may still be fitted, "
      "which would leave the FX3 waiting in its boot ROM. Nothing here is "
      "damaged, and this wizard can simply be run again.</p>");
}
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
